Fabmobil/Pflanzensensor/Pflanzensensor/data/img/cloud_big.png

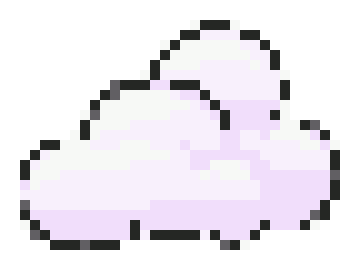
Pflanzensensor/data/img/cloud_big.png
