Fabmobil/Pflanzensensor/Pflanzensensor/data/img/flower_big.gif

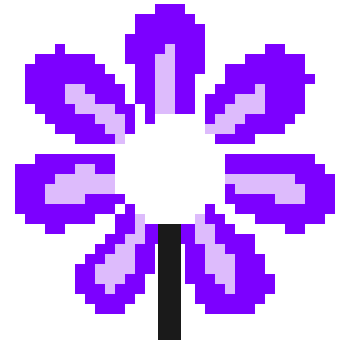
Pflanzensensor/data/img/flower_big.gif
