Fabmobil/Pflanzensensor/Pflanzensensor/src/web/handler/sensor_handler.cpp

/**
 * @file sensor_handler.cpp
 * Fixed version with memory safety improvements
 */

#include "web/handler/sensor_handler.h"

#include <ArduinoJson.h>

#include "logger/logger.h"
#include "managers/manager_config.h"
#include "utils/helper.h"
#include "web/core/components.h"

// Maximum number of values per sensor
static constexpr size_t MAX_VALUES = 10;

bool SensorHandler::ownsUrl(const String& url) {
  // Muss synchron zu onRegisterRoutes() bleiben: die Lazy-Loading-Middleware
  // lädt den Handler nur für hier genannte Pfade, sonst läuft die Anfrage ins
  // 404 statt in die registrierte Route.
  return url == F("/getLatestValues") || url == F("/measure");
}

RouterResult SensorHandler::onRegisterRoutes(WebRouter& router) {
  LOG_DEBUG(F("SensorHandler"), F("Registriere Sensor-Routen"));

  // Register Latest Values endpoint
  auto latestResult =
      router.addRoute(HTTP_GET, "/getLatestValues", [this]() { handleGetLatestValues(); });
  if (!latestResult.isSuccess())
    return latestResult;

  // Sofortmessung von der Startseite aus (ohne Anmeldung, siehe handleMeasure).
  // Bewusst hier und nicht im AdminSensorHandler: dieser Handler liegt wegen
  // /getLatestValues ohnehin im Handler-Cache, solange jemand die Startseite
  // ansieht. Der AdminSensorHandler müsste bei jedem Klick neu gebaut werden
  // und verdrängte dabei andere Handler aus dem Dreier-Cache.
  auto measureResult = router.addRoute(HTTP_POST, "/measure", [this]() { handleMeasure(); });
  if (!measureResult.isSuccess())
    return measureResult;

  return RouterResult::success();
}

void SensorHandler::handleMeasure() {
  // Die Drossel ist funktionslokal statisch, kein Member: der Handler wird vom
  // LRU-Cache des WebManagers jederzeit zerstört und neu gebaut, ein Member
  // vergäße die Sperre dabei und der Endpunkt wäre unbegrenzt aufrufbar.
  static RequestThrottle throttle(MEASURE_MIN_INTERVAL_MS);

  uint32_t freeHeap = ESP.getFreeHeap();
  if (freeHeap < 4096) {
    LOG_WARN(F("SensorHandler"),
             String(F("Nicht genügend Speicher für Sofortmessung: ")) + String(freeHeap));
    sendJsonResponse(503, F("{\"success\":false,\"error\":\"Nicht genügend Speicher\"}"));
    return;
  }

  String sensorId = _server.arg("sensor");
  if (sensorId.length() == 0) {
    sendJsonResponse(400, F("{\"success\":false,\"error\":\"Fehlende Sensor-ID\"}"));
    return;
  }

  // Der Endpunkt ist offen, die ID landet im Log und in der Antwort: alles
  // außer dem Format der echten Sensor-IDs wird gar nicht erst weitergereicht.
  if (sensorId.length() > 32) {
    sendJsonResponse(400, F("{\"success\":false,\"error\":\"Ungültige Sensor-ID\"}"));
    return;
  }
  for (size_t i = 0; i < sensorId.length(); i++) {
    char c = sensorId[i];
    bool erlaubt = (c >= 'A' && c <= 'Z') || (c >= 'a' && c <= 'z') || (c >= '0' && c <= '9') ||
                   c == '_' || c == '-';
    if (!erlaubt) {
      sendJsonResponse(400, F("{\"success\":false,\"error\":\"Ungültige Sensor-ID\"}"));
      return;
    }
  }

  if (!_sensorManager.isHealthy()) {
    sendJsonResponse(503,
                     F("{\"success\":false,\"error\":\"Sensor-Manager nicht betriebsbereit\"}"));
    return;
  }

  Sensor* sensor = _sensorManager.getSensor(sensorId);
  if (!sensor) {
    LOG_WARN(F("SensorHandler"), String(F("Sofortmessung: Sensor nicht gefunden: ")) + sensorId);
    sendJsonResponse(404, F("{\"success\":false,\"error\":\"Sensor nicht gefunden\"}"));
    return;
  }

  // forceImmediateMeasurement() prüft das nicht - ohne diesen Zweig meldete der
  // Server Erfolg und die Oberfläche wartete auf einen Wert, der nie kommt.
  if (!sensor->isEnabled() || !sensor->isInitialized()) {
    sendJsonResponse(409, F("{\"success\":false,\"error\":\"Sensor ist nicht betriebsbereit\"}"));
    return;
  }

  // Eine erzwungene Messung verdrängt den aktuellen Slot-Halter (siehe
  // SensorPreemption). Läuft schon eine, wird nicht noch eine hinterhergeschoben
  // - sonst könnten dauernde Aufrufe die regulären Intervallmessungen aushungern.
  if (_sensorManager.hasForcedMeasurement()) {
    _server.sendHeader(F("Retry-After"), F("5"));
    sendJsonResponse(429, F("{\"success\":false,\"error\":\"Es läuft bereits eine "
                            "Sofortmessung\",\"retryAfterMs\":5000}"));
    return;
  }

  // Die Drossel wird ganz zuletzt gezogen: sie soll die Messung begrenzen, nicht
  // die Fehlerfälle. Ein Aufruf mit unbekannter Sensor-ID sperrt so den nächsten
  // gültigen nicht aus.
  if (!throttle.tryAcquire(millis())) {
    uint32_t restMs = throttle.remaining(millis());
    _server.sendHeader(F("Retry-After"), F("2"));
    sendJsonResponse(429, String(F("{\"success\":false,\"error\":\"Zu viele Anfragen\","
                                   "\"retryAfterMs\":")) +
                              String(restMs) + F("}"));
    return;
  }

  if (!_sensorManager.forceImmediateMeasurement(sensorId)) {
    LOG_ERROR(F("SensorHandler"),
              String(F("Sofortmessung konnte nicht geplant werden: ")) + sensorId);
    sendJsonResponse(500, F("{\"success\":false,\"error\":\"Fehler beim Planen der Messung\"}"));
    return;
  }

  LOG_INFO(F("SensorHandler"), String(F("Sofortmessung von der Startseite: ")) + sensorId);
  sendJsonResponse(200, String(F("{\"success\":true,\"sensor\":\"")) + sensorId +
                            F("\",\"cooldownMs\":") + String(MEASURE_MIN_INTERVAL_MS) + F("}"));
}

HandlerResult SensorHandler::handleGet(const String& /*uri*/,
                                       const std::map<String, String>& /*query*/) {
  // Let registerRoutes handle the actual routing
  return HandlerResult::fail(HandlerError::INVALID_REQUEST, "Bitte verwenden Sie registerRoutes");
}

HandlerResult SensorHandler::handlePost(const String& /*uri*/,
                                        const std::map<String, String>& /*params*/) {
  // Let registerRoutes handle the actual routing
  return HandlerResult::fail(HandlerError::INVALID_REQUEST, "Bitte verwenden Sie registerRoutes");
}

void SensorHandler::handleGetLatestValues() {
  // **CRITICAL FIX 1: Memory check before starting**
  uint32_t freeHeap = ESP.getFreeHeap();
  if (freeHeap < 4096) { // Require at least 4KB free
    LOG_WARN(F("SensorHandler"),
             String(F("Nicht genügend Speicher für JSON-Antwort: ")) + String(freeHeap));
    _server.send(503, F("application/json"), F("{\"error\":\"Nicht genügend Speicher\"}"));
    return;
  }

  beginChunkedResponse(F("application/json"));

  // Send basic info first
  sendChunk(F("{\"currentTime\":"));
  sendChunk(String(millis()));
  sendChunk(F(",\"deviceName\":\""));
  sendChunk(ConfigMgr.getDeviceName());
  sendChunk(F("\",\"flowerStatusSensor\":\""));
  sendChunk(ConfigMgr.getFlowerStatusSensor());
  sendChunk(F("\",\"ip\":\""));
  sendChunk(Component::getDisplayIP());
  sendChunk(F("\",\"sensors\":{"));

  auto managerState = _sensorManager.getState();
  if (managerState != ManagerState::INITIALIZED) {
    LOG_WARN(F("SensorHandler"),
             String(F("Sensormanager nicht initialisiert, Status: ")) + String((int)managerState));
    sendChunk(F("},\"error\":\"Sensormanager nicht initialisiert\"}"));
    endChunkedResponse();
    return;
  }

  const auto& sensors = _sensorManager.getSensors();
  const size_t sensorCount = sensors.size();

  if (sensorCount == 0) {
    LOG_WARN(F("SensorHandler"), F("Keine Sensoren im Sensormanager gefunden"));
    sendChunk(F("},\"error\":\"Keine Sensoren verfügbar\"}"));
    endChunkedResponse();
    return;
  }

  bool firstMeasurement = true;
  size_t processedSensors = 0;

  for (size_t sensorIndex = 0; sensorIndex < sensorCount && sensorIndex < 20; sensorIndex++) {
    if (ESP.getFreeHeap() < 4096) {
      LOG_WARN(F("SensorHandler"), F("Wenig Speicher während der Verarbeitung, Abbruch"));
      break;
    }

    const auto& sensor = sensors[sensorIndex];
    if (!sensor) {
      LOG_WARN(F("SensorHandler"), String(F("Null-Sensor an Index ")) + String(sensorIndex));
      continue;
    }

    if (!sensor->isInitialized()) {
      LOG_WARN(F("SensorHandler"),
               String(F("Überspringe nicht initialisierten Sensor: ")) + sensor->getName());
      continue;
    }

    String sensorName;
    sensorName = sensor->getName();
    if (sensorName.length() == 0) {
      sensorName = String(F("Unbekannt_")) + String(sensorIndex);
    }

    if (!sensor->isEnabled()) {
      LOG_DEBUG(F("SensorHandler"), String(F("Sensor ")) + sensorName + F(" ist deaktiviert"));
      continue;
    }

    MeasurementData measurementData;
    measurementData = sensor->getMeasurementData();

    if (!measurementData.isValid() || measurementData.activeValues == 0) {
      LOG_WARN(F("SensorHandler"), String(F("Ungültige Messdaten für Sensor ")) + sensorName);
      continue;
    }

    // Sensor has never completed a successful measurement yet.
    // Avoid publishing placeholder startup values like 0.0.
    if (sensor->getMeasurementStartTime() == 0) {
      LOG_DEBUG(F("SensorHandler"),
                String(F("Überspringe Sensor ohne erfolgreiche Erstmessung: ")) + sensorName);
      continue;
    }

    size_t safeActiveValues =
        min(measurementData.activeValues, static_cast<size_t>(SensorConfig::MAX_MEASUREMENTS));
    safeActiveValues = min(safeActiveValues, MAX_VALUES);

    for (size_t i = 0; i < safeActiveValues; i++) {
      if (i >= SensorConfig::MAX_MEASUREMENTS || i >= measurementData.values.size() ||
          i >= SensorConfig::MAX_MEASUREMENTS) {
        LOG_WARN(F("SensorHandler"),
                 String(F("Array-Grenzen überschritten für Sensor ")) + sensorName);
        break;
      }

      String fieldName;
      fieldName = measurementData.fieldNames[i];
      if (fieldName.length() == 0) {
        continue;
      }

      fieldName.replace("\"", "");
      fieldName.replace("\n", "");
      fieldName.replace("\r", "");

      if (fieldName.length() > 50) {
        fieldName = fieldName.substring(0, 50);
      }

      float value = 0.0f;
      String unit;
      value = measurementData.values[i];
      unit = measurementData.units[i];

      unit.replace("\"", "");
      unit.replace("\n", "");
      unit.replace("\r", "");
      if (unit.length() > 10) {
        unit = unit.substring(0, 10);
      }

      // Never expose 0 ppm as a valid reading.
      if (unit.equalsIgnoreCase("ppm") && value <= 0.0f) {
        LOG_DEBUG(F("SensorHandler"), String(F("Überspringe ungültigen ppm-Wert für Sensor ")) +
                                          sensorName + String(F(": ")) + String(value, 2));
        continue;
      }

      if (!firstMeasurement) {
        sendChunk(F(","));
      }
      firstMeasurement = false;

      String fieldKey = sensor->getId() + "_" + String(i);
      sendChunk(F("\""));
      sendChunk(fieldKey);
      sendChunk(F("\":{\"value\":"));

      if (!isnan(value) && isfinite(value)) {
        sendChunk(String(value, 2));
      } else {
        sendChunk(F("null"));
      }

      sendChunk(F(",\"unit\":\""));
      sendChunk(unit);
      sendChunk(F("\""));

      sendChunk(F(",\"lastMeasurement\":"));
      sendChunk(String(sensor->getMeasurementStartTime()));
      sendChunk(F(",\"measurementInterval\":"));
      sendChunk(String(sensor->getMeasurementInterval()));
      sendChunk(F(",\"status\":\""));
      sendChunk(sensor->getStatus(i));
      sendChunk(F("\""));

      const auto& config = sensor->config();
      if (i < config.measurements.size()) {
        sendChunk(F(",\"absoluteMin\":"));
        sendChunk(String(config.measurements[i].absoluteMin, 2));
        sendChunk(F(",\"absoluteMax\":"));
        sendChunk(String(config.measurements[i].absoluteMax, 2));
      }

#if USE_ANALOG
      if (isAnalogSensor(sensor.get())) {
        AnalogSensor* analog = static_cast<AnalogSensor*>(sensor.get());
        int rawValue = analog->getLastRawValue(i);
        sendChunk(F(",\"raw\":"));
        sendChunk(String(rawValue));

        const auto& analogCfg = sensor->config();
        if (i < analogCfg.measurements.size()) {
          // If historical raw extrema are still the sentinel values, and
          // autocalibration is active, present the active calculation
          // limits as a UI-friendly fallback so the admin page shows
          // values instead of "--". This does NOT overwrite persisted
          // historical extrema on disk.
          int effectiveRawMin = analogCfg.measurements[i].absoluteRawMin;
          int effectiveRawMax = analogCfg.measurements[i].absoluteRawMax;
          if ((effectiveRawMin == INT_MAX || effectiveRawMax == INT_MIN) &&
              analogCfg.measurements[i].calibrationMode) {
            if (analog) {
              float calcMin = analog->getMinValue(i);
              float calcMax = analog->getMaxValue(i);
              if (effectiveRawMin == INT_MAX)
                effectiveRawMin = static_cast<int>(roundf(calcMin));
              if (effectiveRawMax == INT_MIN)
                effectiveRawMax = static_cast<int>(roundf(calcMax));
            }
          }
          sendChunk(F(",\"absoluteRawMin\":"));
          sendChunk(String(effectiveRawMin));
          sendChunk(F(",\"absoluteRawMax\":"));
          sendChunk(String(effectiveRawMax));
          sendChunk(F(",\"calibrationMode\":"));
          sendChunk(analogCfg.measurements[i].calibrationMode ? F("true") : F("false"));
          // Also include the active calculation limits (min/max) used for
          // mapping so the admin UI can reflect autocal changes in real time.
          AnalogSensor* analogPtr = static_cast<AnalogSensor*>(sensor.get());
          if (analogPtr) {
            float calcMin = analogPtr->getMinValue(i);
            float calcMax = analogPtr->getMaxValue(i);
            sendChunk(F(",\"minmax\":{"));
            sendChunk(F("\"min\":"));
            sendChunk(String(calcMin));
            sendChunk(F(",\"max\":"));
            sendChunk(String(calcMax));
            sendChunk(F("}"));
          }
          // Note: autocalization now persists into the calculation limits
          // (min/max). The historical extremum storage (absoluteRawMin/Max)
          // remains untouched by autocal and reflects measured history only.
        }
      }
#endif

      sendChunk(F("}"));
    }

    processedSensors++;

    yield();
#ifndef ESP32
    ESP.wdtFeed();
#endif
  }

  sendChunk(F("}"));

  sendChunk(F(",\"system\":{\"freeHeap\":"));
  sendChunk(String(ESP.getFreeHeap()));
  sendChunk(F(",\"heapFragmentation\":"));
#ifdef ESP32
  uint32_t heapFrag =
      ESP.getFreeHeap() > 0 ? (100 - (ESP.getMaxAllocHeap() * 100 / ESP.getFreeHeap())) : 0;
  sendChunk(String(heapFrag));
#else
  sendChunk(String(ESP.getHeapFragmentation()));
#endif
  sendChunk(F(",\"rebootCount\":"));
  sendChunk(String(Helper::getRebootCount()));
  sendChunk(F(",\"version\":\""));
  sendChunk(VERSION);
  sendChunk(F("\",\"buildDate\":\""));
  sendChunk(F(__DATE__));
  sendChunk(F("\",\"processedSensors\":"));
  sendChunk(String(processedSensors));
  sendChunk(F("}}"));

  endChunkedResponse();
}

bool SensorHandler::validateRequest() const {
  return true; // Sensorendpunkte sind öffentlich
}
