Fabmobil/Pflanzensensor/Pflanzensensor/src/sensors/sensor_analog.h

/**
 * @file sensor_analog.h
 * @brief Analog sensor class for analog value measurement
 */

#ifndef SENSOR_ANALOG_H
#define SENSOR_ANALOG_H

#include "sensor_analog_multiplexer.h"
#include "sensors/sensor_autocalibration.h"
#include "sensors/sensors.h"

// Forward declarations
class SensorPersistence;

#if USE_ANALOG

/**
 * @brief Configuration structure for analog sensors
 *
 * Holds all configuration parameters needed for analog sensor operation
 * including pin assignments, multiplexer settings, and calibration values.
 */
struct AnalogConfig : public SensorConfig {
  // ACHTUNG: pin und minimumDelay NICHT hier deklarieren - beide existieren
  // bereits in SensorConfig. Eigene Member gleichen Namens hätten die
  // Basis-Member verdeckt: der Konstruktor hätte die abgeleiteten gesetzt,
  // während Sensor::m_tempConfig = config beim Slicing nur die Basis kopiert -
  // und die wäre auf 0 geblieben. Genau das war der Fall: die konfigurierten
  // 500 ms Mindestabstand zwischen Einzelmessungen wurden bei Analogsensoren
  // stillschweigend ignoriert, weil Sensor::performMeasurementCycle() auf
  // config().minimumDelay == 0 traf.
  bool useMultiplexer; ///< Whether to use multiplexer for multiple inputs

  /**
   * @brief Default constructor for AnalogConfig
   * @details Sets id to 'ANALOG'.
   */
  AnalogConfig() : SensorConfig(), useMultiplexer(USE_MULTIPLEXER) {
    name = F("Analog Sensor");
    id = F("ANALOG"); // Unified ID
    pin = ANALOG_PIN;
    activeMeasurements = ANALOG_SENSOR_COUNT;
    if (measurementInterval == 0)
      measurementInterval = ANALOG_MEASUREMENT_INTERVAL * 1000;
    minimumDelay = ANALOG_MINIMUM_DELAY;

    // Set min/max and inverted for each measurement in MeasurementConfig
    for (size_t i = 0; i < activeMeasurements && i < measurements.size(); ++i) {
      switch (i) {
      case 0:
        measurements[i].name = ANALOG_1_NAME;
        measurements[i].fieldName = ANALOG_1_FIELD_NAME;
        measurements[i].unit = ANALOG_1_UNIT;
        measurements[i].minValue = ANALOG_1_MIN;
        measurements[i].maxValue = ANALOG_1_MAX;
        measurements[i].inverted = ANALOG_1_INVERTED;
        measurements[i].calibrationMode = ANALOG_1_CALIBRATION_MODE;
        measurements[i].limits.yellowLow = ANALOG_1_YELLOW_LOW;
        measurements[i].limits.greenLow = ANALOG_1_GREEN_LOW;
        measurements[i].limits.greenHigh = ANALOG_1_GREEN_HIGH;
        measurements[i].limits.yellowHigh = ANALOG_1_YELLOW_HIGH;
        break;
#if ANALOG_SENSOR_COUNT > 1
      case 1:
        measurements[i].name = ANALOG_2_NAME;
        measurements[i].fieldName = ANALOG_2_FIELD_NAME;
        measurements[i].unit = ANALOG_2_UNIT;
        measurements[i].minValue = ANALOG_2_MIN;
        measurements[i].maxValue = ANALOG_2_MAX;
        measurements[i].inverted = ANALOG_2_INVERTED;
        measurements[i].calibrationMode = ANALOG_2_CALIBRATION_MODE;
        measurements[i].limits.yellowLow = ANALOG_2_YELLOW_LOW;
        measurements[i].limits.greenLow = ANALOG_2_GREEN_LOW;
        measurements[i].limits.greenHigh = ANALOG_2_GREEN_HIGH;
        measurements[i].limits.yellowHigh = ANALOG_2_YELLOW_HIGH;
        break;
#endif
#if ANALOG_SENSOR_COUNT > 2
      case 2:
        measurements[i].name = ANALOG_3_NAME;
        measurements[i].fieldName = ANALOG_3_FIELD_NAME;
        measurements[i].unit = ANALOG_3_UNIT;
        measurements[i].minValue = ANALOG_3_MIN;
        measurements[i].maxValue = ANALOG_3_MAX;
        measurements[i].inverted = ANALOG_3_INVERTED;
        measurements[i].calibrationMode = ANALOG_3_CALIBRATION_MODE;
        measurements[i].limits.yellowLow = ANALOG_3_YELLOW_LOW;
        measurements[i].limits.greenLow = ANALOG_3_GREEN_LOW;
        measurements[i].limits.greenHigh = ANALOG_3_GREEN_HIGH;
        measurements[i].limits.yellowHigh = ANALOG_3_YELLOW_HIGH;
        break;
#endif
#if ANALOG_SENSOR_COUNT > 3
      case 3:
        measurements[i].name = ANALOG_4_NAME;
        measurements[i].fieldName = ANALOG_4_FIELD_NAME;
        measurements[i].unit = ANALOG_4_UNIT;
        measurements[i].minValue = ANALOG_4_MIN;
        measurements[i].maxValue = ANALOG_4_MAX;
        measurements[i].inverted = ANALOG_4_INVERTED;
        measurements[i].calibrationMode = ANALOG_4_CALIBRATION_MODE;
        measurements[i].limits.yellowLow = ANALOG_4_YELLOW_LOW;
        measurements[i].limits.greenLow = ANALOG_4_GREEN_LOW;
        measurements[i].limits.greenHigh = ANALOG_4_GREEN_HIGH;
        measurements[i].limits.yellowHigh = ANALOG_4_YELLOW_HIGH;
        break;
#endif
#if ANALOG_SENSOR_COUNT > 4
      case 4:
        measurements[i].name = ANALOG_5_NAME;
        measurements[i].fieldName = ANALOG_5_FIELD_NAME;
        measurements[i].unit = ANALOG_5_UNIT;
        measurements[i].minValue = ANALOG_5_MIN;
        measurements[i].maxValue = ANALOG_5_MAX;
        measurements[i].inverted = ANALOG_5_INVERTED;
        measurements[i].calibrationMode = ANALOG_5_CALIBRATION_MODE;
        measurements[i].limits.yellowLow = ANALOG_5_YELLOW_LOW;
        measurements[i].limits.greenLow = ANALOG_5_GREEN_LOW;
        measurements[i].limits.greenHigh = ANALOG_5_GREEN_HIGH;
        measurements[i].limits.yellowHigh = ANALOG_5_YELLOW_HIGH;
        break;
#endif
#if ANALOG_SENSOR_COUNT > 5
      case 5:
        measurements[i].name = ANALOG_6_NAME;
        measurements[i].fieldName = ANALOG_6_FIELD_NAME;
        measurements[i].unit = ANALOG_6_UNIT;
        measurements[i].minValue = ANALOG_6_MIN;
        measurements[i].maxValue = ANALOG_6_MAX;
        measurements[i].inverted = ANALOG_6_INVERTED;
        measurements[i].calibrationMode = ANALOG_6_CALIBRATION_MODE;
        measurements[i].limits.yellowLow = ANALOG_6_YELLOW_LOW;
        measurements[i].limits.greenLow = ANALOG_6_GREEN_LOW;
        measurements[i].limits.greenHigh = ANALOG_6_GREEN_HIGH;
        measurements[i].limits.yellowHigh = ANALOG_6_YELLOW_HIGH;
        break;
#endif
#if ANALOG_SENSOR_COUNT > 6
      case 6:
        measurements[i].name = ANALOG_7_NAME;
        measurements[i].fieldName = ANALOG_7_FIELD_NAME;
        measurements[i].unit = ANALOG_7_UNIT;
        measurements[i].minValue = ANALOG_7_MIN;
        measurements[i].maxValue = ANALOG_7_MAX;
        measurements[i].inverted = ANALOG_7_INVERTED;
        measurements[i].calibrationMode = ANALOG_7_CALIBRATION_MODE;
        measurements[i].limits.yellowLow = ANALOG_7_YELLOW_LOW;
        measurements[i].limits.greenLow = ANALOG_7_GREEN_LOW;
        measurements[i].limits.greenHigh = ANALOG_7_GREEN_HIGH;
        measurements[i].limits.yellowHigh = ANALOG_7_YELLOW_HIGH;
        break;
#endif
#if ANALOG_SENSOR_COUNT > 7
      case 7:
        measurements[i].name = ANALOG_8_NAME;
        measurements[i].fieldName = ANALOG_8_FIELD_NAME;
        measurements[i].unit = ANALOG_8_UNIT;
        measurements[i].minValue = ANALOG_8_MIN;
        measurements[i].maxValue = ANALOG_8_MAX;
        measurements[i].inverted = ANALOG_8_INVERTED;
        measurements[i].calibrationMode = ANALOG_8_CALIBRATION_MODE;
        measurements[i].limits.yellowLow = ANALOG_8_YELLOW_LOW;
        measurements[i].limits.greenLow = ANALOG_8_GREEN_LOW;
        measurements[i].limits.greenHigh = ANALOG_8_GREEN_HIGH;
        measurements[i].limits.yellowHigh = ANALOG_8_YELLOW_HIGH;
        break;
#endif
      default:
        measurements[i].name = "";
        measurements[i].fieldName = "";
        measurements[i].unit = "%";
        measurements[i].minValue = 0.0f;
        measurements[i].maxValue = 0.0f;
        measurements[i].inverted = false;
        measurements[i].calibrationMode = false;
        measurements[i].limits.yellowLow = 0.0f;
        measurements[i].limits.greenLow = 0.0f;
        measurements[i].limits.greenHigh = 100.0f;
        measurements[i].limits.yellowHigh = 100.0f;
        break;
      }
      // DO NOT initialize raw min/max values here - let JSON loading handle it
      // This prevents constructor values from overriding loaded JSON values
    }
  }
};

/**
 * @brief Class handling analog sensor operations
 *
 * Manages analog sensor initialization, measurement, and data processing
 * with support for multiplexed inputs and configurable sampling.
 */
class AnalogSensor : public Sensor {
public:
  /**
   * @brief Constructs an analog sensor instance
   * @param config The configuration for this analog sensor
   * @param sensorManager Reference to the sensor manager
   */
  explicit AnalogSensor(const AnalogConfig& config, class SensorManager* sensorManager);

  /**
   * @brief Initializes the analog sensor hardware
   * @return SensorResult indicating success or failure with error details
   * @override
   */
  SensorResult init() override;

  /**
   * @brief Begins a new measurement cycle
   * @return SensorResult indicating success or failure with error details
   * @override
   */
  SensorResult startMeasurement() override;

  /**
   * @brief Continues an in-progress measurement
   * @return SensorResult indicating success, failure, or measurement completion
   * @override
   */
  SensorResult continueMeasurement() override;

  /**
   * @brief Cleans up and releases hardware resources
   * @override
   */
  void deinitialize() override;

  /**
   * @brief Validates a measurement value
   * @param value The value to validate
   * @return true if value is valid, false otherwise
   * @override
   */
  bool isValidValue(float value) const override {
    return !isnan(value) && value >= 0.0f && value <= 100.0f;
  }

  /**
   * @brief Validates a measurement value for a specific index
   * @param value The value to validate
   * @param measurementIndex The index of the measurement
   * @return true if value is valid, false otherwise
   * @override
   */
  bool isValidValue(float value, size_t measurementIndex) const override {
    return isValidValue(value);
  }

  /**
   * @brief Gets information about shared hardware resources
   * @return SharedHardwareInfo structure with resource details
   * @override
   */
  SharedHardwareInfo getSharedHardwareInfo() const override {
    return SharedHardwareInfo(SensorType::ANALOG_SENSOR, config().pin, config().minimumDelay);
  }

  /**
   * @brief Destructor
   * @override
   */
  ~AnalogSensor() override;

  /**
   * @brief Fetch a single sample for a given analog channel
   * @param value Reference to store the sample
   * @param index Channel index
   * @return true if successful, false if hardware error
   *
   * @note For inverted sensors (inverted=true), the mapping is flipped:
   *       high raw values result in low percentages and vice versa.
   *       This is useful for sensors like soil moisture where high
   *       resistance (high raw value) means low moisture (low percentage).
   */
  bool fetchSample(float& value, size_t index) override;

  /**
   * @brief Log sensor-specific debug details
   */
  void logDebugDetails() const override;

  /**
   * @brief Get the minimum value for a given channel
   * @param idx Channel index
   * @return Minimum value
   */
  inline float getMinValue(size_t idx) const {
    if (idx < config().measurements.size()) {
      const auto& m = config().measurements[idx];
      // Bei aktiver Autokalibrierung gilt die laufend angepasste Untergrenze.
      // (Früher wurde hier zusätzlich eine zweite Config gegengeprüft, weil der
      // Sensor eine eigene Kopie hielt und beide auseinanderlaufen konnten.)
      if (m.calibrationMode)
        return static_cast<float>(m.autocal.min_value);
      return m.minValue;
    }
    return 0.0f;
  }
  /**
   * @brief Set the minimum value for a given channel
   * @param idx Channel index
   * @param v Minimum value to set
   */
  inline void setMinValue(size_t idx, float v) {
    if (idx < mutableConfig().measurements.size())
      mutableConfig().measurements[idx].minValue = v;
  }
  /**
   * @brief Get the maximum value for a given channel
   * @param idx Channel index
   * @return Maximum value
   */
  inline float getMaxValue(size_t idx) const {
    if (idx < config().measurements.size()) {
      const auto& m = config().measurements[idx];
      if (m.calibrationMode)
        return static_cast<float>(m.autocal.max_value);
      return m.maxValue;
    }
    return 0.0f;
  }
  /**
   * @brief Set the maximum value for a given channel
   * @param idx Channel index
   * @param v Maximum value to set
   */
  inline void setMaxValue(size_t idx, float v) {
    if (idx < mutableConfig().measurements.size())
      mutableConfig().measurements[idx].maxValue = v;
  }
  /**
   * @brief Get the last raw ADC value for a given channel
   * @param idx Channel index
   * @return Last raw ADC value, or -1 if unavailable
   */
  inline int getLastRawValue(size_t idx) const {
    return (idx < m_lastRawValues.size()) ? m_lastRawValues[idx] : -1;
  }

  /**
   * @brief Set the absolute raw minimum value for a given channel
   * @param idx Channel index
   * @param rawMin Absolute raw minimum value to set
   */
  inline void setAbsoluteRawMin(size_t idx, int rawMin) {
    if (idx < mutableConfig().measurements.size())
      mutableConfig().measurements[idx].absoluteRawMin = rawMin;
  }

  /**
   * @brief Set the absolute raw maximum value for a given channel
   * @param idx Channel index
   * @param rawMax Absolute raw maximum value to set
   */
  inline void setAbsoluteRawMax(size_t idx, int rawMax) {
    if (idx < mutableConfig().measurements.size())
      mutableConfig().measurements[idx].absoluteRawMax = rawMax;
  }

  /**
   * @brief Set the autocalibration state for a given channel
   * @param idx Channel index
   * @param cal AutoCal struct to set
   */
  inline void setAutoCalibration(size_t idx, const AutoCal& cal) {
    if (idx < mutableConfig().measurements.size())
      mutableConfig().measurements[idx].autocal = cal;
  }

  /**
   * @brief Set or clear the autocalibration runtime flag for a channel
   * @details This updates the sensor's internal runtime copy of the
   * measurement configuration so measurement-time logic (like clamping)
   * observes the calibration mode immediately.
   */
  inline void setCalibrationMode(size_t idx, bool enabled) {
    if (idx < mutableConfig().measurements.size())
      mutableConfig().measurements[idx].calibrationMode = enabled;
  }

  /**
   * @brief Get the autocalibration state for a given channel
   */
  inline AutoCal getAutoCalibration(size_t idx) const {
    if (idx < config().measurements.size())
      return config().measurements[idx].autocal;
    return AutoCal();
  }

  /**
   * @brief Get autocal min/max quickly (uint16_t)
   */
  inline uint16_t getAutoCalMin(size_t idx) const {
    if (idx < config().measurements.size())
      return config().measurements[idx].autocal.min_value;
    return 0;
  }
  inline uint16_t getAutoCalMax(size_t idx) const {
    if (idx < config().measurements.size())
      return config().measurements[idx].autocal.max_value;
    return 1023;
  }

protected:
  /**
   * @brief Returns the number of measurements for this analog sensor (clamped
   * to MAX_MEASUREMENTS)
   */
  size_t getNumMeasurements() const override {
    return std::min(config().activeMeasurements,
                    static_cast<size_t>(SensorConfig::MAX_MEASUREMENTS));
  }

private:
  // Es gibt bewusst KEINE eigene AnalogConfig-Kopie mehr.
  //
  // AnalogSensor hielt früher zusätzlich zu Sensor::m_tempConfig eine eigene
  // vollständige AnalogConfig - inklusive des std::array<MeasurementConfig, 8>,
  // also rund 900 Byte samt 24 Heap-Strings. Beide Kopien mussten von Hand
  // synchron gehalten werden, was sich durch den ganzen Sensor zog
  // (doppelte Schreibvorgänge in fetchSample(), Abgleiche wie
  // "m.calibrationMode || cfgCal"). Jetzt ist config()/mutableConfig() der
  // Basisklasse die einzige Quelle der Wahrheit.
  bool m_useMultiplexer; ///< Ob ein Multiplexer verwendet wird (kein Basis-Member)

  // Hardware interface
#if USE_MULTIPLEXER
  std::unique_ptr<Multiplexer> m_multiplexer;
#endif

  // Store last raw ADC value per channel
  std::vector<int> m_lastRawValues;
  // Track if clamping warning was already shown in this measurement cycle
  std::vector<bool> m_clampWarningShown;

  // Only keep DRY-compliant helpers
  bool validateReading(int reading, size_t measurementIndex) const;

  /**
   * @brief Maps raw analog values to percentage values
   * @param rawValue The raw ADC reading
   * @param measurementIndex The index of the measurement configuration
   * @return Mapped percentage value (0-100%)
   *
   * @note For inverted sensors, the mapping is flipped so that high raw values
   *       result in low percentages. This is useful for sensors like soil
   *       moisture where high resistance (high raw value) means low moisture.
   */
  float mapAnalogValue(int rawValue, size_t measurementIndex) const;

  bool canAccessHardware() const;
};

#endif // USE_ANALOG
#endif // SENSOR_ANALOG_H
