Fabmobil/Pflanzensensor/Pflanzensensor/src/web/handler/admin_sensor_handler_routing.cpp

/**
 * @file admin_sensor_handler_routing.cpp
 * @brief Implementation of routing and basic request handling
 */

#include "admin_sensor_handler.h"
#include "logger/logger.h"

// WICHTIG: ownsUrl() und onRegisterRoutes() müssen dieselben Pfade nennen.
// Sie stehen bewusst direkt untereinander - vorher lag die Liste, für die der
// Handler geladen wird, in der Lazy-Loading-Middleware des WebManagers. Beide
// Listen sind auseinandergelaufen: der Handler registrierte 13 Routen, die
// Middleware lud ihn nur für 3 davon. Die übrigen 9 lieferten nach einem
// frischen Boot 404, solange niemand vorher /admin/sensors aufgerufen hatte.
bool AdminSensorHandler::ownsUrl(const String& url) {
  return url == F("/admin/sensors") || url == F("/admin/sensor_update") ||
         url == F("/admin/measurement_interval") || url == F("/admin/analog_minmax") ||
         url == F("/admin/analog_autocal") || url == F("/admin/analog_autocal_duration") ||
         url == F("/admin/thresholds") || url == F("/admin/measurement_name") ||
         url == F("/admin/reset_absolute_minmax") || url == F("/admin/reset_absolute_raw_minmax") ||
         url == F("/trigger_measurement") || url == F("/admin/getSensorConfig");
}

RouterResult AdminSensorHandler::onRegisterRoutes(WebRouter& router) {
  LOG_DEBUG(F("AdminSensorHandler"), F("Registriere Admin-Sensor-Routen"));

  auto result = router.addRoute(HTTP_GET, "/admin/sensors", [this]() {
    LOG_DEBUG(F("AdminSensorHandler"), F("GET /admin/sensors aufgerufen"));
    handleSensorConfig();
  });
  if (!result.isSuccess()) {
    LOG_ERROR(F("AdminSensorHandler"),
              String(F("Registrieren von GET /admin/sensors fehlgeschlagen: ")) +
                  result.getMessage());
    return result;
  }

  result = router.addRoute(HTTP_POST, "/admin/sensors", [this]() {
    LOG_DEBUG(F("AdminSensorHandler"), F("POST /admin/sensors aufgerufen"));
    handleSensorUpdate();
  });
  if (!result.isSuccess()) {
    LOG_ERROR(F("AdminSensorHandler"),
              String(F("Registrieren von POST /admin/sensors fehlgeschlagen: ")) +
                  result.getMessage());
    return result;
  }

  // Note: /admin/sensors/flower_status removed - use unified /admin/config/setConfigValue
  // with namespace="general", key="flower_sens"

  result = router.addRoute(HTTP_POST, "/admin/sensor_update", [this]() {
    LOG_DEBUG(F("AdminSensorHandler"), F("POST /admin/sensor_update aufgerufen"));
    handleSingleSensorUpdate();
  });
  if (!result.isSuccess()) {
    LOG_ERROR(F("AdminSensorHandler"),
              String(F("Registrieren von POST /admin/sensor_update fehlgeschlagen: ")) +
                  result.getMessage());
    return result;
  }

  result = router.addRoute(HTTP_POST, "/admin/measurement_interval", [this]() {
    LOG_DEBUG(F("AdminSensorHandler"), F("POST /admin/measurement_interval aufgerufen"));
    handleMeasurementInterval();
  });
  if (!result.isSuccess()) {
    LOG_ERROR(F("AdminSensorHandler"),
              String(F("Registrieren von POST /admin/measurement_interval fehlgeschlagen: ")) +
                  result.getMessage());
    return result;
  }

#if USE_ANALOG
  result = router.addRoute(HTTP_POST, "/admin/analog_minmax", [this]() {
    LOG_DEBUG(F("AdminSensorHandler"), F("POST /admin/analog_minmax aufgerufen"));
    handleAnalogMinMax();
  });
  if (!result.isSuccess()) {
    LOG_ERROR(F("AdminSensorHandler"),
              String(F("Registrieren von POST /admin/analog_minmax fehlgeschlagen: ")) +
                  result.getMessage());
    return result;
  }

  result = router.addRoute(HTTP_POST, "/admin/analog_autocal", [this]() {
    LOG_DEBUG(F("AdminSensorHandler"), F("POST /admin/analog_autocal aufgerufen"));
    handleAnalogAutocal();
  });
  if (!result.isSuccess()) {
    LOG_ERROR(F("AdminSensorHandler"),
              String(F("Registrieren von POST /admin/analog_autocal fehlgeschlagen: ")) +
                  result.getMessage());
    return result;
  }

  result = router.addRoute(HTTP_POST, "/admin/analog_autocal_duration", [this]() {
    LOG_DEBUG(F("AdminSensorHandler"), F("POST /admin/analog_autocal_duration aufgerufen"));
    handleAnalogAutocalDuration();
  });
  if (!result.isSuccess()) {
    LOG_ERROR(F("AdminSensorHandler"),
              String(F("Registrieren von POST /admin/analog_autocal_duration fehlgeschlagen: ")) +
                  result.getMessage());
    return result;
  }
#endif

  result = router.addRoute(HTTP_POST, "/admin/thresholds", [this]() {
    LOG_DEBUG(F("AdminSensorHandler"), F("POST /admin/thresholds aufgerufen"));
    handleThresholds();
  });
  if (!result.isSuccess()) {
    LOG_ERROR(F("AdminSensorHandler"),
              String(F("Registrieren von POST /admin/thresholds fehlgeschlagen: ")) +
                  result.getMessage());
    return result;
  }

  result = router.addRoute(HTTP_POST, "/admin/measurement_name", [this]() {
    LOG_DEBUG(F("AdminSensorHandler"), F("POST /admin/measurement_name aufgerufen"));
    handleMeasurementName();
  });
  if (!result.isSuccess()) {
    LOG_ERROR(F("AdminSensorHandler"),
              String(F("Registrieren von POST /admin/measurement_name fehlgeschlagen: ")) +
                  result.getMessage());
    return result;
  }

  result = router.addRoute(HTTP_POST, "/admin/reset_absolute_minmax", [this]() {
    LOG_DEBUG(F("AdminSensorHandler"), F("POST /admin/reset_absolute_minmax aufgerufen"));
    handleResetAbsoluteMinMax();
  });
  if (!result.isSuccess()) {
    LOG_ERROR(F("AdminSensorHandler"),
              String(F("Registrieren von POST /admin/reset_absolute_minmax fehlgeschlagen: ")) +
                  result.getMessage());
    return result;
  }

  result = router.addRoute(HTTP_POST, "/admin/reset_absolute_raw_minmax", [this]() {
    LOG_DEBUG(F("AdminSensorHandler"), F("POST /admin/reset_absolute_raw_minmax aufgerufen"));
    handleResetAbsoluteRawMinMax();
  });
  if (!result.isSuccess()) {
    LOG_ERROR(F("AdminSensorHandler"),
              String(F("Registrieren von POST /admin/reset_absolute_raw_minmax fehlgeschlagen: ")) +
                  result.getMessage());
    return result;
  }

  // /admin/reset_autocal removed: redundant with reset_absolute_raw_minmax/reset_absolute_minmax
  // Route intentionally not registered to avoid exposing duplicate functionality

  result = router.addRoute(HTTP_POST, "/trigger_measurement", [this]() {
    LOG_DEBUG(F("AdminSensorHandler"), F("POST /trigger_measurement aufgerufen"));
    handleTriggerMeasurement();
  });
  if (!result.isSuccess()) {
    LOG_ERROR(F("AdminSensorHandler"),
              String(F("Registrieren von POST /trigger_measurement fehlgeschlagen: ")) +
                  result.getMessage());
    return result;
  }

  result = router.addRoute(HTTP_GET, "/admin/getSensorConfig", [this]() {
    LOG_DEBUG(F("AdminSensorHandler"), F("GET /admin/getSensorConfig aufgerufen"));
    handleGetSensorConfigJson();
  });
  if (!result.isSuccess()) {
    LOG_ERROR(F("AdminSensorHandler"),
              String(F("Registrieren von GET /admin/getSensorConfig fehlgeschlagen: ")) +
                  result.getMessage());
    return result;
  }

  return RouterResult::success();
}

HandlerResult AdminSensorHandler::handleGet(const String& uri,
                                            const std::map<String, String>& query) {
  if (uri == "/admin/sensors") {
    handleSensorConfig();
    return HandlerResult::success();
  }
  return HandlerResult::fail(HandlerError::NOT_FOUND, "Unbekannter Endpunkt");
}

HandlerResult AdminSensorHandler::handlePost(const String& uri,
                                             const std::map<String, String>& params) {
  if (uri == "/admin/sensors") {
    handleSensorUpdate();
    return HandlerResult::success();
  } else if (uri == "/trigger_measurement") {
    handleTriggerMeasurement();
    return HandlerResult::success();
  }
  // Note: /admin/sensors/flower_status removed - use unified /admin/config/setConfigValue
  return HandlerResult::fail(HandlerError::NOT_FOUND, "Unbekannter Endpunkt");
}
