Fabmobil/Pflanzensensor/Pflanzensensor/src/managers/manager_config.cpp

/**
 * @file manager_config.cpp
 * @brief Implementation of the simplified ConfigManager class
 */

#include "manager_config.h"

#include "../logger/logger.h"
#include "../managers/manager_config_persistence.h"
#include "../managers/manager_resource.h"
#include "../managers/manager_sensor.h"
#include "../managers/manager_sensor_persistence.h"
#include "../utils/critical_section.h"
#include "../utils/flash_persistence.h"
#include "../utils/mail_scheduler.h"
#include "../web/handler/admin_handler.h"
#include "../web/handler/web_ota_handler.h"
#include "managers/manager_config_preferences.h"

#if USE_DISPLAY
#include "managers/manager_display.h"
// Forward declaration
extern std::unique_ptr<DisplayManager> displayManager;
#endif

ConfigManager::ConfigManager() : m_debugConfig(m_notifier), m_sensorErrorTracker(m_notifier) {}

ConfigManager& ConfigManager::getInstance() {
  static ConfigManager instance;
  return instance;
}

ConfigManager::ConfigResult ConfigManager::loadConfig() {

  // Load and apply log level from Preferences FIRST, before loading other
  // config This ensures the correct log level is active for all subsequent log
  // messages
  String logLevel =
      PreferencesManager::getString(PreferencesNamespaces::LOG, "level", String(LOG_LEVEL));
  logger.setLogLevel(Logger::stringToLogLevel(logLevel));
  LOG_DEBUG(F("ConfigM"), String(F("Log-Level geladen: ")) + logLevel);

  // Load main configuration
  auto result = ConfigPersistence::load(m_configData);
  if (!result.isSuccess()) {
    return ConfigResult::fail(result.error().value_or(ConfigError::UNKNOWN_ERROR),
                              result.getMessage());
  }

  // Sync subsystem data
  syncSubsystemData();

  // Validate loaded config (non-fatal - warn but continue)
  auto validationResult = ConfigValidator::validateConfigData(m_configData);
  if (!validationResult.isSuccess()) {
    LOG_WARN(F("ConfigM"), String(F("Geladene Konfiguration hat Validierungsprobleme: ")) +
                               validationResult.getMessage());
  }

  notifyConfigChange("config", "loaded", false);
  m_configLoaded = true;

  // Apply logging settings
  logger.enableFileLogging(m_configData.fileLoggingEnabled);

  return ConfigResult::success();
}

ConfigManager::ConfigResult ConfigManager::saveConfig() {

  // Sync data from subsystems back to main config
  m_debugConfig.saveToConfigData(m_configData);

  // Validate before saving
  auto validationResult = ConfigValidator::validateConfigData(m_configData);
  if (!validationResult.isSuccess()) {
    LOG_ERROR(F("ConfigM"), String(F("Konfigurationsvalidierung fehlgeschlagen: ")) +
                                validationResult.getMessage());
    return ConfigResult::fail(validationResult.error().value_or(ConfigError::UNKNOWN_ERROR),
                              validationResult.getMessage());
  }

  // Save main configuration
  auto result = ConfigPersistence::save(m_configData);
  if (!result.isSuccess()) {
    return ConfigResult::fail(result.error().value_or(ConfigError::UNKNOWN_ERROR),
                              result.getMessage());
  }

  // Save sensor configuration
  auto sensorResult = SensorPersistence::save();
  if (!sensorResult.isSuccess()) {
    LOG_WARN(F("ConfigM"), String(F("Speichern der Sensorkonfiguration fehlgeschlagen: ")) +
                               sensorResult.getMessage());
    // Continue even if sensor config save fails
  }

  return ConfigResult::success();
}

ConfigManager::ConfigResult ConfigManager::resetToDefaults() {

  auto result = ConfigPersistence::resetToDefaults(m_configData);
  if (!result.isSuccess()) {
    return ConfigResult::fail(result.error().value_or(ConfigError::UNKNOWN_ERROR),
                              result.getMessage());
  }

  // Sync subsystem data
  syncSubsystemData();

  // Ensure in-memory config reflects compile-time defaults for items that
  // should be reset immediately (device name, etc.). We intentionally do
  // NOT persist these values here to avoid re-creating a config file from
  // in-memory values after the persistence layer deleted it. The Admin
  // handler will perform the reboot after rendering a confirmation page.
  m_configData.deviceName = String(DEVICE_NAME);

  notifyConfigChange("config", "reset", true);
  // Do not call saveConfig() here — that could re-write the deleted
  // config.json with current in-memory values. The caller (web UI) will
  // trigger a reboot so the device boots with empty storage and will use
  // compile-time defaults on next load.
  return ConfigResult::success();
}

ConfigManager::ConfigResult ConfigManager::setAdminPassword(const String& password) {

  auto validation = ConfigValidator::validatePassword(password);
  if (!validation.isSuccess()) {
    return ConfigResult::fail(validation.error().value_or(ConfigError::UNKNOWN_ERROR),
                              validation.getMessage());
  }

  if (m_configData.adminPassword != password) {
    m_configData.adminPassword = password;
    auto saveResult = PreferencesManager::updateStringValue(PreferencesNamespaces::GENERAL,
                                                            "admin_pwd", password);
    if (!saveResult.isSuccess()) {
      return ConfigResult::fail(saveResult.error().value_or(ConfigError::SAVE_FAILED),
                                saveResult.getMessage());
    }
    notifyConfigChange("admin_password", "updated", true);
  }
  return ConfigResult::success();
}

ConfigManager::ConfigResult ConfigManager::setMD5Verification(bool enabled) {
  return updateBoolConfig(
      m_configData.md5Verification, enabled,
      [](bool val) {
        return PreferencesManager::updateBoolValue(PreferencesNamespaces::GENERAL, "md5_verify",
                                                   val);
      },
      "md5_verification", true);
}

ConfigManager::ConfigResult ConfigManager::setDebugMail(bool enabled) {
  return updateBoolConfig(
      m_configData.debugMail, enabled,
      [](bool val) {
        return PreferencesManager::updateBoolValue(PreferencesNamespaces::DEBUG, "mail", val);
      },
      F("Debug Mail"));
}

// === Mailversand ===
//
// Alle Werte liegen im Namensraum "general" mit dem Präfix "mail_". Ein eigener
// Namensraum wäre auf LittleFS ein Verzeichnis und kostete 16 KB Metadaten -
// zwei Segmente Chronik, nur für den Ordnernamen.

bool ConfigManager::isMailSensorWatched(const String& key) const {
  // Die Vergleichslogik steht in utils/mail_scheduler.h, weil sie dort ohne
  // Hardware geprüft werden kann - "DHT_1" darf nicht in "DHT_10" treffen.
  return Mail::isWatched(m_configData.mailSensors.c_str(), key.c_str());
}
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
